jvanstraten/gated-clock/primitives/cross/README.md

Cross-wire primitive
====================

This is a simple `X` "circuit" used in the inter-NAND-gate routing of the
flipflops.
