jvanstraten/gated-clock/primitives/jumper/README.md

2-way jumper-based switch
=========================

This is a single-component primitive for a Harwin M50-3530342 1.27mm pitch
3-pin header, used for the 50/60Hz jumper configuration.
