jvanstraten/gated-clock/subcircuits/div5_n/README.md

Divide by 5, no output
======================

This circuit performs a frequency division by 5. This variant only divides, no
output pins are provided. Specifically, this circuit is used for the division
of the incoming 50/60Hz clock from the grid. To make everything line up at the
top, the outline extends an extra 9.25mm to the left; this bit is manually
routed in the mainboard primitive.

Circuit:

```
ClkIn~1 Arn~1         Arn~2           ClkIn~2 Arn~3         Arn~4           ClkIn~3 Arn~5         Arn~6           ClkOut
      | | .----..       |                   | | .----..       |                   | | .----..       |               |
      | '-|A     \      |      ,-.          | '-|A     \      |      ,-.          | '-|A     \      |      ,-.      |
    .-)---|4   P3 |()-. |     |   |---.   .-)---|4   P3 |()-. |     |   |---.   .-)---|4   P3 |()-. |     |   |---. |
    | | .-|1     /    | |      `-'    |   | | .-|1     /    | |      `-'    |   | | .-|1     /    | |      `-'    | |
    | | | '----''     | |             |   | | | '----''     | |             |   | | | '----''     | |             | |
    | | '-----.,------' |             |   | | '-----.,------' |             |   | | '-----.,------' |             | |
    | | .-----'`------. |             |   | | .-----'`------. |             |   | | .-----'`------. |             | |
    | | | .----..     | | .----..     |   | | | .----..     | | .----..     |   | | | .----..     | | .----..     | |
    | | '-|3     \    | '-|A     \    |   | | '-|3     \    | '-|A     \    |   | | '-|3     \    | '-|A     \    | |
    | |   |    P1 |()-o---|1   Qn |()-)-. | |   |    P1 |()-o---|1   Qn |()-)-. | |   |    P1 |()-o---|1   Qn |()-)-o
    | o---|C     /    | .-|Q     /    | | | o---|C     /    | .-|Q     /    | | | o---|C     /    | .-|Q     /    | |
    | |   '----''     | | '----''     | | | |   '----''     | | '----''     | | | |   '----''     | | '----''     | |
    | |  _____________| '-----.,------)-o | |  _____________| '-----.,------)-o | |  _____________| '-----.,------)-o
    | | |               .-----'`------o | | | |               .-----'`------o | | | |               .-----'`------o |
    | | | .----..       | .----..     | | | | | .----..       | .----..     | | | | | .----..       | .----..     | |
    | | '-|1     \      '-|Qn    \    | | | | '-|1     \      '-|Qn    \    | | | | '-|1     \      '-|Qn    \    | |
    | '---|C   P2 |()-.   |     Q |()-' | | '---|C   P2 |()-.   |     Q |()-' | | '---|C   P2 |()-.   |     Q |()-' |
    '---o-|4     /    o---|2     /      | '---o-|4     /    o---|2     /      | '---o-|4     /    o---|2     /      |
        | '----''     |   '----''       |     | '----''     |   '----''       |     | '----''     |   '----''       |
        '-----.,------'                 |     '-----.,------'                 |     '-----.,------'                 |
        .-----'`------.                 |     .-----'`------.                 |     .-----'`------.                 |
        | .----..     |                 |     | .----..     |                 |     | .----..     |                 |
        '-|2     \    |                 |     '-|2     \    |                 |     '-|2     \    |                 |
          |    P4 |()-'                 |       |    P4 |()-'                 |       |    P4 |()-'                 |
        .-|Dn    /          ..----.     '-------|Dn    /                      o-------|Dn    /                      |
        | '----''          /  d5cn|---.         '----''                       |       '----''                       |
        '---------------()| fb    |   '---------------------------------------'                                     |
                           \  d5bn|---------------------------------------------------------------------------------'
                            ''----'
```

Total width, not including borders, is:

 - 6 gates x 8mm = 48mm;
 - 26 wiring spacers x 1.5mm = 39mm;
 - total 87mm.
