jvanstraten/gated-clock/subcircuits/div5or6_n/README.md

Divide by 5 or 6, no output
===========================

This circuit performs a frequency division by 5, or 6 depending on the
configuration of the two DIP switches. The circuit either behaves as a single
div5 (jumpers in the upper/outer positions) or as a div3 followed by a div2
(jumpers in the lower/inner positions).

Circuit:

```
ClkIn~1 Arn~1         Arn~2           ClkIn~2 Arn~3         Arn~4          ClkIn~3 Arn~5          Arn~6           ClkOut
      | | .----..       |                   | | .----..       |               |     | .----..       |               |
      | '-|A     \      |      ,-.          | '-|A     \      |      ,-.      |     '-|A     \      |      ,-.      |
    .-)---|4   P3 |()-. |     |   |---.   .-)---|4   P3 |()-. |     |   |---. | .-----|4   P3 |()-. |     |   |---. |
    | | .-|1     /    | |      `-'    |   | | .-|1     /    | |      `-'    | | |   .-|1     /    | |      `-'    | |
    | | | '----''     | |             |   | | | '----''     | |             ||O||   | '----''     | |             | |
    | | '-----.,------' |             |   | | '-----.,------' |             ||O|)-. '-----.,------' |             | |
    | | .-----'`------. |             |   | | .-----'`------. |             ||O|| | .-----'`------. |             | |
    | | | .----..     | | .----..     |   | | | .----..     | | .----..     | | | | | .----..     | | .----..     | |
    | | '-|3     \    | '-|A     \    |   | | '-|3     \    | '-|A     \    | | | | '-|3     \    | '-|A     \    | |
    | |   |    P1 |()-o---|1   Qn |()-)-. | |   |    P1 |()-o---|1   Qn |()-)-o | |   |    P1 |()-o---|1   Qn |()-)-o
    | o---|C     /    | .-|Q     /    | | | o---|C     /    | .-|Q     /    | | | o---|C     /    | .-|Q     /    | |
    | |   '----''     | | '----''     | | | |   '----''     | | '----''     | | | |   '----''     | | '----''     | |
    | |  _____________| '-----.,------)-o | |  _____________| '-----.,------)-o | |  _____________| '-----.,------)-o
    | | |               .-----'`------o | | | |               .-----'`------o | | | |               .-----'`------o |
    | | | .----..       | .----..     | | | | | .----..       | .----..     | | | | | .----..       | .----..     | |
    | | '-|1     \      '-|Qn    \    | | | | '-|1     \      '-|Qn    \    | | | | '-|1     \      '-|Qn    \    | |
    | '---|C   P2 |()-.   |     Q |()-' | | '---|C   P2 |()-.   |     Q |()-' | | '---|C   P2 |()-.   |     Q |()-o |
    '---o-|4     /    o---|2     /      | '---o-|4     /    o---|2     /      | '---o-|4     /    o---|2     /    | |
        | '----''     |   '----''       |     | '----''     |   '----''       |     | '----''     |   '----''     | |
        '-----.,------'         _       |     '-----.,------'             _   |     '-----.,------'               | |
        .-----'`------.        |O|----. |     .-----'`------.       50Hz |O|--o     .-----'`------.               | |
        | .----..     |        |O|--. | |     | .----..     |            |O|--)---. | .----..     |               | |
        '-|2     \    |        |O|--)-)-o     '-|2     \    |       60Hz |O|--)-. | '-|2     \    |               | |
          |    P4 |()-'             | | |       |    P4 |()-'                 | | |   |    P4 |()-'               | |
        .-|Dn    /          ..----. | | '-------|Dn    /                (3x)  | | '---|Dn    /                    | |
        | '----''          /  d5xn|-' |         '----''                       | |     '----''                     | |
        '---------------()| fb    | .-)---------------------------------------' '---------------------------------' |
                           \  d5bn|-' '-----------------------------------------------------------------------------'
                            ''----'
```

Total width, not including borders, is:

 - 6 gates x 8mm = 48mm;
 - 26 wiring spacers x 1.5mm = 39mm;
 - total 87mm.
