jvanstraten/gated-clock/subcircuits/div5/README.md

Divide by 5
===========

This circuit performs a frequency division by 5. Note that the output order is
not regular binary.

Order:

```
    .-----.-----.-----.---------.
    | d5c | d5b | d5a | decimal |
.---+-----+-----+-----+---------|
| 0 |  0  |  0  |  0  |    0    |
| 1 |  0  |  0  |  1  |    1    |
| 2 |  0  |  1  |  1  |    3    |
| 3 |  1  |  1  |  0  |    6    |
| 4 |  1  |  0  |  0  |    4    |
'---'-----'-----'-----'---------'
```

Circuit:

```
ClkIn~1 Arn~1         Arn~2           ClkIn~2 Arn~3         Arn~4           ClkIn~3 Arn~5         Arn~6           ClkOut
      | | .----..       |                   | | .----..       |                   | | .----..       |               |
      | '-|A     \      |      ,-.          | '-|A     \      |      ,-.          | '-|A     \      |      ,-.      |
    .-)---|4   P3 |()-. |     |   |---.   .-)---|4   P3 |()-. |     |   |---.   .-)---|4   P3 |()-. |     |   |---. |
    | | .-|1     /    | |      `-'    |   | | .-|1     /    | |      `-'    |   | | .-|1     /    | |      `-'    | |
    | | | '----''     | |             |   | | | '----''     | |             |   | | | '----''     | |             | |
    | | '-----.,------' |             |   | | '-----.,------' |             |   | | '-----.,------' |             | |
    | | .-----'`------. |             |   | | .-----'`------. |             |   | | .-----'`------. |             | |
    | | | .----..     | | .----..     |   | | | .----..     | | .----..     |   | | | .----..     | | .----..     | |
    | | '-|3     \    | '-|A     \    |   | | '-|3     \    | '-|A     \    |   | | '-|3     \    | '-|A     \    | |
    | |   |    P1 |()-o---|1   Qn |()-)-. | |   |    P1 |()-o---|1   Qn |()-)-. | |   |    P1 |()-o---|1   Qn |()-)-o
    | o---|C     /    | .-|Q     /    | | | o---|C     /    | .-|Q     /    | | | o---|C     /    | .-|Q     /    | |
    | |   '----''     | | '----''     | | | |   '----''     | | '----''     | | | |   '----''     | | '----''     | |
    | |  _____________| '-----.,------)-o | |  _____________| '-----.,------)-o | |  _____________| '-----.,------)-o
    | | |               .-----'`------o | | | |               .-----'`------o | | | |               .-----'`------o |
    | | | .----..       | .----..     | | | | | .----..       | .----..     | | | | | .----..       | .----..     | |
    | | '-|1     \      '-|Qn    \    | | | | '-|1     \      '-|Qn    \    | | | | '-|1     \      '-|Qn    \    | |
    | '---|C   P2 |()-.   |     Q |()-o | | '---|C   P2 |()-.   |     Q |()-o | | '---|C   P2 |()-.   |     Q |()-' |
    '---o-|4     /    o---|2     /    | | '---o-|4     /    o---|2     /    | | '---o-|4     /    o---|2     /      |
        | '----''     |   '----''     | |     | '----''     |   '----''     | |     | '----''     |   '----''       |
        '-----.,------'               | |     '-----.,------'               | |     '-----.,------'                 |
        .-----'`------.               | |     .-----'`------.               | |     .-----'`------.                 |
        | .----..     |               | |     | .----..     |               | |     | .----..     |                 |
        '-|2     \    |               | |     '-|2     \    |               | |     '-|2     \    |                 |
          |    P4 |()-'               | |       |    P4 |()-'               | |       |    P4 |()-'                 |
        .-|Dn    /          ..----.   | o-------|Dn    /                    | o-------|Dn    /                      |
        | '----''          /  d5cn|---)-)-.     '----''                     | |       '----''                       |
        '---------------()| fb    |   | | '---------------------------------)-o                                     |
                           \  d5bn|---)-)-----------------------------------)-)-------------------------------------o
                            ''----'   | |                                   | |                                     |
                                   d5ap d5an                             d5bp d5bn                                  d5cn
```

Total width, not including borders, is:

 - 6 gates x 8mm = 48mm;
 - 26 wiring spacers x 1.5mm = 39mm;
 - total 87mm.
