jvanstraten/gated-clock/notes/power-input.asc

C1: cap; 100n
C2: cap; 100n
C3: cap; 100n
D3: diode
D4: diode
R1: res; 1meg
R2: res; 10k
R3: res; 100k
R4: res; 47
R5: res; 1
R6: res; 10k
R7: res; 16k9
R8: res; 10k
R9: res; 100
R10: res; 470
U1: 4N25
U2: LT1006
V1: voltage; PULSE(-305 305 0 8ms 8ms 2ms 20ms 50)
V2: voltage; 3V3
V3: voltage; SINE(0 100 50 4ms)
V4: voltage; PULSE(0 400 0.95 1u)
V5: voltage; 9
Named nets: 0
.tran 0 1 0.9
