jvanstraten/gated-clock/notes/TPS26631.asc

I1: current; SINE(0 150n 1000)
I2: current; SINE(0 150n 900)
I3: current; SINE(0 150n 1000)
R1: res; 16k9
R2: res; 1k27
R3: res; 5k11
R4: res; 16k9
R5: res; 5k11
R6: res; 680
V1: voltage; PULSE(4 6 0 2)
V2: voltage; 1.2
V3: voltage; 1.1.2
V4: voltage; PULSE(0.9 1.5 0.5 1us 1us 1s)
Named nets: 0
.tran 2
