jvanstraten/gated-clock/notes/synchroscope-led-drive.asc

D1: LED; NSCW100
D2: LED; NSCW100
D3: LED; NSCW100
D4: LED; NSCW100
I1: current; SINE(5m 3m 1)
Q1: pnp; 2N4403
Q2: pnp; 2N4403
Q3: pnp; 2N4403
Q4: pnp; 2N4403
Q5: pnp; 2N4403
Q6: pnp; 2N4403
Q7: pnp; 2N4403
R1: res; 1k
R2: res; 1k
R3: res; 1k
R4: res; 1k
R5: res; 10k
R6: res; 10k
R7: res; 470
R8: res; 100
R9: res; 100k
R10: res; 100k
V1: voltage; PULSE(0 5 0 10u 10u 1 5)
V2: voltage; 0.3
V3: voltage; PULSE(0 5 0 10u 10u 2 5)
V4: voltage; 0
V5: voltage; PULSE(0 5 0 10u 10u 3 5)
V6: voltage; 0
V7: voltage; PULSE(0 5 0 10u 10u 4 5)
V8: voltage; 0
V9: voltage; 5
V10: voltage; PULSE(5 0 0 10us 10us 10ms 20ms)
V11: voltage; PULSE(5 0 5ms 10us 10us 10ms 20ms)
Named nets: 0
.tran 5
1 TLC6C5748-Q1 channel
No PWM, always on
Teensy PWM 1
Teensy PWM 2
