jvanstraten/gated-clock/notes/led-drive.asc

B1: bi; I=(sin(time*10)*0.003 + 0.005)*(sin(time*1000)>0)
C1: cap; 100n
C2: cap; 1n
D1: LED; NSCW100
D2: LED; NSCW100
D3: LED; NSCW100
D4: LED; NSCW100
I2: current; SINE(8mA 8mA 30Hz)
Q1: pnp; 2N4403
Q2: pnp; 2N4403
Q3: pnp; 2N4403
Q4: pnp; 2N4403
Q5: pnp; 2N4403
R1: res; 1k
R2: res; 1k
R3: res; 1k
R4: res; 1k
R5: res; 100
R6: res; 10k
R7: res; 470
R8: res; 1k
R9: res; 10k
U1: LT1006
V1: voltage; PULSE(0 5 0 10u 10u 1 5)
V2: voltage; 0.3
V3: voltage; PULSE(0 5 0 10u 10u 2 5)
V4: voltage; 0
V5: voltage; PULSE(0 5 0 10u 10u 3 5)
V6: voltage; 0
V7: voltage; PULSE(0 5 0 10u 10u 4 5)
V8: voltage; 0
V9: voltage; 5
V10: voltage; 5V
Named nets: 0
.tran 5
1 TLC6C5748-Q1 channel
