jvanstraten/gated-clock/notes/synchroscope-leds.asc

D1: diode
D2: diode
D3: diode
D4: diode
D5: diode
D6: diode
Q1: pnp
Q2: pnp
Q3: pnp
R1: res; 680
R2: res; 680
R3: res; 680
V1: voltage; PULSE(0 5 0 1ms 1ms 2s 3s)
V2: voltage; PULSE(0 5 1s 1ms 1ms 2s 3s)
V3: voltage; PULSE(0 5 2s 1ms 1ms 2s 3s)
V4: voltage; PULSE(5 0 0 1ms 1ms 3s 6s)
V5: voltage; PULSE(5 0 2s 1ms 1ms 3s 6s)
V6: voltage; PULSE(5 0 4s 1ms 1ms 3s 6s)
V7: voltage; SINE(3.5 1.5 3 0)
V8: voltage; SINE(3.5 1.5 3 0.5)
Named nets: 0
.tran 0 12 6
