jvanstraten/gated-clock/notes/tline.asc

C1: cap; 3pF; V=5 Irms=1 Rser=0.015 Lser=450p
C2: cap; 27p; V=5 Irms=1 Rser=0.015 Lser=450p
C3: cap; 2420pf
C4: cap; 1980pF
C5: cap; 197pF
C6: cap; 363pF
O1: ltline; MyLossyTline
O2: ltline; MyLossyTline
O3: ltline; MyLossyTline
O4: ltline; MyLossyTline
O5: ltline; MyLossyTline
O6: ltline; MyLossyTline
O7: ltline; MyLossyTline
R1: res; 101
R2: res; 4.5
R3: res; 1
R4: res; 4.5
R5: res; 37
R6: res; 99
R7: res; 17
R8: res; 1k
R9: res; 1k
R10: res; 1010
R11: res; 990
S1: sw; switch
S2: sw; switch
V1: voltage; PULSE(0 5 3.6ns 2.5ns)
V2: voltage; 5
V3: voltage; PULSE(0 5 1ns 0.5ns)
Named nets: 0
.tran 0 1000ns 0 0.1ns
.model MyLossyTline LTRA(len=50 R=0.00238 L=2.3e-10 C=1.462e-13)
.model switch SW(Ron=1 Roff=1Meg Vt=0.01)
297pF - 363pF
1980pF - 2420pF
