jvanstraten/gated-clock/firmware/src/timezones.hpp

#include <inttypes.h>
static const uint32_t TIMEZONES[3885] = {
    0x00000011,
    0x00000021,
    0x00000001,
    0x00000031,
    0x00000011,
    0x2A6A2003,
    0x2A8F2011,
    0x2C5A2003,
    0x2C872011,
    0x2E521803,
    0x2E7D2011,
    0x30491803,
    0x306D2011,
    0x32361803,
    0x32652011,
    0x342E1803,
    0x34551811,
    0x36261803,
    0x364D1811,
    0x38161803,
    0x38441811,
    0x3A0D1803,
    0x3A311811,
    0x3B7D1803,
    0x3C291811,
    0x3D751803,
    0x3E211811,
    0x3F6D1803,
    0x40111811,
    0x415B1803,
    0x42081811,
    0x43531803,
    0x43781811,
    0x45441803,
    0x45701811,
    0x473B1803,
    0x47681811,
    0x49322003,
    0x49561811,
    0x4B232003,
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
};
