jvanstraten/gated-clock/firmware/src/led.hpp

#include <inttypes.h>

#pragma once

/**
 * TLC6C5748 LED controller namespace.
 */
namespace led {

// Pin number definitions.
static const int PIN_SIN  =  0;
static const int PIN_SOUT =  1;
static const int PIN_LAT  =  6;
static const int PIN_OVER = 13;
static const int PIN_SCLK = 20;

/**
 * A single RGB channel of a TLC6C5748.
 */
struct Channel {

    /**
     * PWM-based brightness configuration, 0..65535.
     */
    uint16_t pwm_r;
    uint16_t pwm_g;
    uint16_t pwm_b;

    /**
     * Analog brightness configuration, ranges from 0..127 for 25..100%.
     */
    uint8_t dc_r;
    uint8_t dc_g;
    uint8_t dc_b;

    /**
     * Whether to enable this segment when display override is active. That is,
     * PWM is overridden to zero when display_override is set and this flag is
     * cleared.
     */
    bool enable;

    /**
     * LED failure detection. When a LED is turned off by discrete logic, it
     * reports as open.
     */
    bool open_r;
    bool open_g;
    bool open_b;
    bool short_r;
    bool short_g;
    bool short_b;

};

/**
 * State data structure for a complete TLC6C5748.
 */
struct Controller {

    /**
     * Channel configuration.
     */
    Channel ch[16];

    /**
     * Maximum current, 0..7. Design point is 1.
     */
    uint8_t mc_r;
    uint8_t mc_g;
    uint8_t mc_b;

    /**
     * Brightness control for a complete color group, essentially multiplied
     * with MC, ranges from 0..127 for 10..100%.
     */
    uint8_t bc_r;
    uint8_t bc_g;
    uint8_t bc_b;

    /**
     * When set, Automatically repeats the 488Hz grayscale cycle, instead of
     * turning the LEDs off after a single cycle.
     */
    bool dsprpt;

    /**
     * When latched, resets the grayscale timing.
     */
    bool tmgrst;

    /**
     * When set, brightness latch update is postponed to the next 488Hz
     * grayscale cycle.
     */
    bool rfresh;

    /**
     * When set, enables enhanced-spectrum PWM, raising it to about 60kHz.
     * Prevents audible whine.
     */
    bool espwm;

    /**
     * Controls whether LEDs are considered open at 70% or 90% Vcc.
     */
    bool lsdvlt;

};

/**
 * LED controller configuration structures.
 */
extern Controller config[3];

/**
 * Controller index for the hours 7-segment displays.
 */
static const uint8_t HOURS_CTRL = 0;

/**
 * Controller index for the minutes 7-segment displays.
 */
static const uint8_t MINUTES_CTRL = 1;

/**
 * Controller index for the seconds 7-segment displays.
 */
static const uint8_t SECONDS_CTRL = 2;

/**
 * Controller channels for the tens 7-segment displays.
 */
static const uint8_t TENS_CH[7] = {1, 5, 12, 9, 8, 0, 4};

/**
 * Controller channels for the units 7-segment displays.
 */
static const uint8_t UNITS_CH[7] = {2, 3, 11, 10, 15, 6, 7};

/**
 * Controller indices for the left and right colons.
 */
static const uint8_t COLON_CTRL[2] = {0, 2};

/**
 * Controller channels for the lower and upper part of the colons.
 */
static const uint8_t COLON_CH[2] = {14, 13};

/**
 * X coordinates for 7-segment display segments.
 */
static const uint8_t SEG_X[7] = {1, 2, 2, 1, 0, 0, 1};

/**
 * Y coordinates for 7-segment display segments.
 */
static const uint8_t SEG_Y[7] = {0, 1, 3, 4, 3, 1, 2};

/**
 * Y coordinates for the colon segments.
 */
static const uint8_t COLON_Y[7] = {3, 1};

/**
 * LED controller index for the status LED.
 */
static const uint8_t STATUS_CTRL = 1;

/**
 * LED controller channel for the status LED.
 */
static const uint8_t STATUS_CH = 14;

/**
 * LED controller index for gate, flipflop, and synchroscope LED brightness.
 */
static const uint8_t BRIGHTNESS_CTRL = 1;

/**
 * LED controller channel for gate, flipflop, and synchroscope LED brightness.
 */
static const uint8_t BRIGHTNESS_CH = 13;

/**
 * Whether to enable the display override signal.
 */
extern bool display_override;

/**
 * Displayed hours in UTC.
 */
extern uint8_t displayed_hours;

/**
 * Displayed minutes in UTC.
 */
extern uint8_t displayed_minutes;

/**
 * Displayed seconds in UTC.
 */
extern uint8_t displayed_seconds;

/**
 * Displayed time validity.
 */
extern bool displayed_time_valid;

/**
 * Sets the text on the display, enabling override. Specify an empty string or
 * nullptr to disable override.
 */
void set_text(const char *text);

/**
 * Sets the color of the display with hue, dark PWM level, light PWM level,
 * dot correction value, and hue delta per X coord and per Y coord (for a
 * rainbow-y effect, because why not?). In addition, es specifies whether the
 * seconds digits should be enabled or not.
 */
void set_color(uint16_t h, uint16_t d, uint16_t l, uint8_t dc, bool es, int16_t hx=0, int16_t hy=0);

/**
 * Sets up pins related to LED control.
 */
void setup();

/**
 * Updates the continuous bit-banged data transfer between the LED controllers
 * and the configuration structure. Returns true when a full sequence was
 * completed (this takes a while, so it's divided up into multiple updates).
 */
bool update();

} // namespace led
