jvanstraten/gated-clock/firmware/src/sine_tab.hpp

#include <inttypes.h>

#pragma once

namespace sine {

static const int16_t SINE[256] = {
    0x0065,
    0x012E,
    0x01F7,
    0x02C0,
    0x0389,
    0x0452,
    0x051B,
    0x05E3,
    0x06AC,
    0x0775,
    0x083E,
    0x0906,
    0x09CF,
    0x0A97,
    0x0B5F,
    0x0C28,
    0x0CF0,
    0x0DB8,
    0x0E80,
    0x0F47,
    0x100F,
    0x10D6,
    0x119D,
    0x1264,
    0x132B,
    0x13F2,
    0x14B9,
    0x157F,
    0x1645,
    0x170B,
    0x17D0,
    0x1896,
    0x195B,
    0x1A20,
    0x1AE5,
    0x1BA9,
    0x1C6D,
    0x1D31,
    0x1DF5,
    0x1EB8,
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
};

} // namespace sine
